AlexIII/gsmGuard/img/proto.jpg

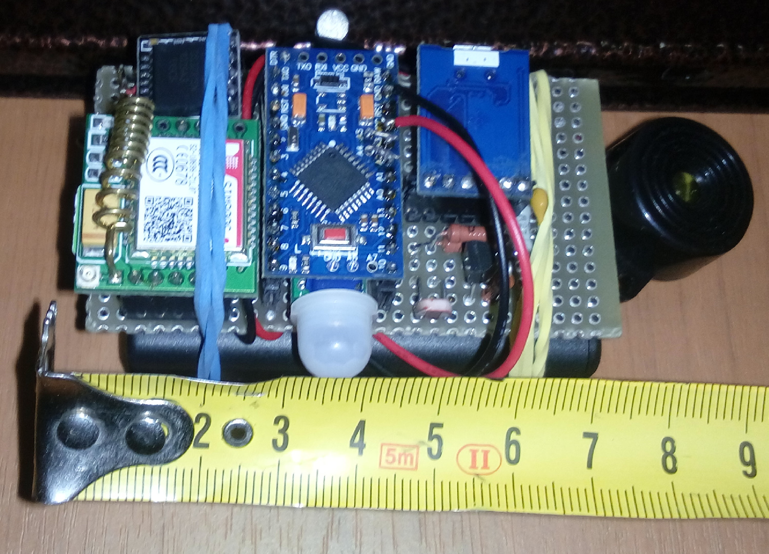
img/proto.jpg
