AlexIII/gsmGuard/gsmGuard-firmware/Config.h

/*
 * GsmGuard v1.0
 * author: github.com/AlexIII
 * e-mail: endoftheworld@bk.ru
 * license: MIT
 */

#ifndef _CONFIG_H_
#define _CONFIG_H_

#include <base64.hpp>
#include <EEvar.h>
#include "Hardware.h"
#include "Event.h"

class Config {
private:
  uint8_t crc;
  uint8_t calcCRC() const {
    uint8_t tmp = 0;
    const uint8_t* data = (const uint8_t*)this + sizeof(crc);
    for(uint16_t i = 0; i < sizeof(*this) - sizeof(crc); ++i)
      tmp += *data++;
    return tmp;
  }
public:
  bool chkCRC() { return crc == calcCRC(); }
public:
  constexpr static uint8_t scheduleMaxSize = 15;
  char phoneNumber[15];
  char lang[3]; //not used
  char dailyReportTime[6];
  int8_t minTemp;
  int8_t maxTemp;
  struct {
    bool maxOneReportIn20min  : 1;
    bool tempAlarmIsOn        : 1;
  private:
    uint8_t reserved          : 6;
  } flags;

  struct SchEntry {
    uint8_t days;
    enum EventSource : uint8_t {
      DOOR_OPEN     = 1<<Event::DOOR_OPEN,
      MOVEMENT      = 1<<Event::MOVEMENT,
      LIGHT_CHANGE  = 1<<Event::LIGHT_CHANGED
    };
    EventSource src;
    Event::Action act;
    uint16_t fromMin;
    uint16_t toMin;

    bool isActive() const {
      const DateTime now = Hardware::now();
      const uint8_t dw = (now.dayOfTheWeek()+6)%7;
      const uint16_t nowMins = now.hour()*60UL + now.minute();
      if(days&(1<<dw)) //if day of the week is right
        if(fromMin == toMin || (nowMins >= fromMin && nowMins < toMin)) //and time is right
          return true;
      return false;
    }
    Event::Action getAction(const SchEntry::EventSource e) const {
      return src & e? act : Event::NO_ACTION;
    }
  };
  uint8_t scheduleSize;
  SchEntry schedule[scheduleMaxSize];

  Config() {}
  Event::Action getAction(const SchEntry::EventSource e) const {
    for(uint8_t i = 0; i < scheduleSize; ++i) {
      const SchEntry &cur = schedule[scheduleSize-i-1];
      DBG(F("SE"), i, cur.src, cur.act);
      if(cur.isActive()) {
        DBG(F("MATCH!"));
        return cur.getAction(e);
      }
      DBG(F("NO FIT"));
    }
    return Event::NO_ACTION;
  }
  Event::Action getAction(const Event &e) const {
    if(e.n > Event::LIGHT_CHANGED) return Event::SMS;
    return getAction(SchEntry::EventSource(1<<e.n));
  }
};

class ConfigSerial : public Config {
  constexpr static int mySz() {
    return sizeof(ConfigSerial) - sizeof(ConfigSerial::store);
  }
public:
  ConfigSerial() { store >> *this; }
  bool formBASE64(const char* str) {
    if(decode_base64_length((uint8_t*)str) != mySz()) {
      DBG(F("Received config: wrong size. Abort."));
      return false;
    }
    decode_base64((uint8_t*)str, (uint8_t*)this);
    if(!chkCRC()) {
      store >> *this;
      DBG(F("Received config: wrong crc. Abort."));
      return false;
    }
    store << *this;
    Hardware::setTime(time);
    return true;
  }
  void toBASE64(Stream &s) {
    const uint16_t len = encode_base64_length(mySz())+1;
    char buff[len];
    strcpy(time, "DD.MM.YY hh:mm:ss");
    Hardware::now().format(time);
    encode_base64((uint8_t*)this, mySz(), (uint8_t*)buff);
    s.write(buff);
  }  
private:
  char time[21];  
  EEstore<Config> store;
};

#endif
